Smartich0ke/Artichoke-LettuceLab-rev1/pcb-files/megasheild4.jpg

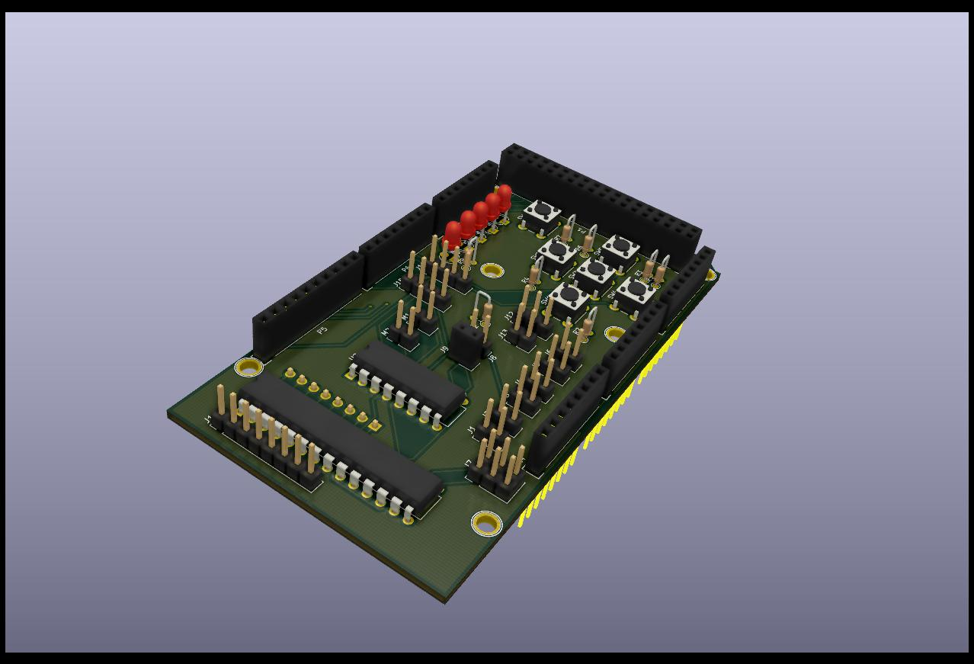
pcb-files/megasheild4.jpg
