Smartich0ke/Artichoke-LettuceLab-rev1/pcb-files/megasheild.png

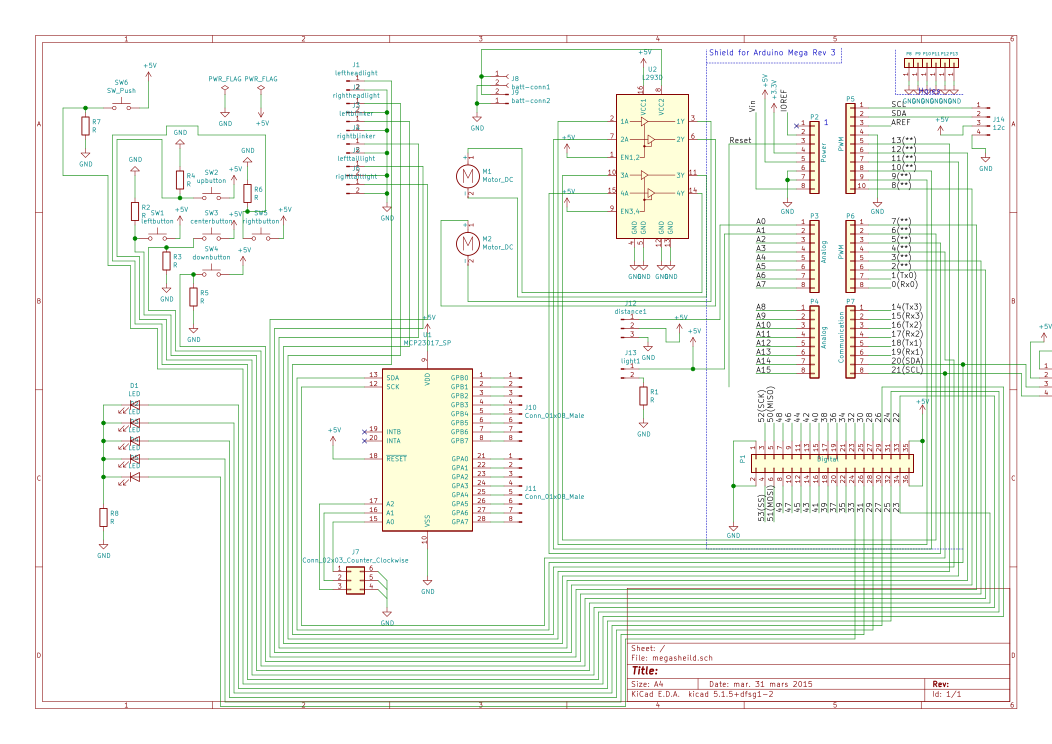
pcb-files/megasheild.png
